m0khz/Simple_VFO/Software_Simple_VFO_Plus_V1_01/display_functions.h

 /*
 * ***********************************************************************************
 * Copyright (c) 2020  M0KHZ - Kevin Wheatley
 * 
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
 * ***********************************************************************************
*/

#include "_fonts.h"

//
//-----------------------------------------------------------------------------
//  Screensaver display
//-----------------------------------------------------------------------------
//
void splashscreen(void)
{
  
   tft.writeRect(0,0,320,240,(uint16_t*)image_240_320); // Draw a pretty picture on screen

}

void rectangle(int x, int y, int w, int d, uint16_t color) 
{
  tft.drawRect(x, y, w, d, color);
}


void display_main_screen(void)
{
  // Clear display area just in case we have 'artifacts' from Sig gen screen

  // now clear the display
  tft.fillScreen(ILI9341_BLACK);
  // draw boarder around full display
  rectangle(outline_boarder_x, outline_boarder_y, outline_boarder_w, outline_boarder_d, outline_boarder_colour);

  // draw rectangle around frequency display
 tft.drawRoundRect(main_freq_boarder_x,main_freq_boarder_y,main_freq_boarder_w,main_freq_boarder_d,3,ILI9341_DARKGREY);

  // clear frequency text area just incase there is something there!
  tft.fillRect((main_freq_boarder_x +1),(main_freq_boarder_y + 1), (main_freq_boarder_w - 3), (main_freq_boarder_d - 2), ILI9341_BLACK);

  // draw rectangle around frequency display
  tft.drawRoundRect(sub_freq_boarder_x,sub_freq_boarder_y,sub_freq_boarder_w,sub_freq_boarder_d,3,ILI9341_DARKGREY);

  // clear frequency text area just incase there is something there!
  tft.fillRect((sub_freq_boarder_x +1),(sub_freq_boarder_y + 1), (sub_freq_boarder_w - 3), (sub_freq_boarder_d - 2), ILI9341_BLACK);

   // draw rectangle around frequency display
   tft.drawRoundRect(info_boarder_x,info_boarder_y,info_boarder_w,info_boarder_d,3,ILI9341_DARKGREY);

  // Now display a user message while system is initialising
  tft.fillRect((info_boarder_x +1),(info_boarder_y + 1), (info_boarder_w - 3), (info_boarder_d - 2), ILI9341_BLACK);
  tft.setCursor(info_cursor_pos_x + 30,info_cursor_pos_y + 10); 
  tft.setTextColor(info_text_colour);
  // set frequency readout font size
  tft.setFont(DroidSansMono_12);
  tft.print("Initialising system");
  // redraw vfo lock if needed
  display_vfo_lock(); 
  
  flag.fg_ReDraw_Screen= true;
  flag.fg_A_B_changed=true;
  flag.fg_freq_Changed=true;

}

// Draw frequency multiplier bar on display
void Freq_Multi_Bar (){
if(flag.mode == false) { // were're in VFO mode so update accordingly

  if(flag.freq_multi_bar){
     
       if(u.tune_multi==1){
        tft.fillRect(20,96,220,2,ILI9341_BLACK );
        tft.fillRect(20,150,220,2,ILI9341_BLACK );
        
          if(flag.vfo_A_active==true){
            tft.fillRect(223,96,14,2,ILI9341_CYAN );
          }
          if(flag.vfo_B_active==true){
            tft.fillRect(223,150,14,2,ILI9341_CYAN );
          }  
       }
       
       if(u.tune_multi==2){
        tft.fillRect(20,96,220,2,ILI9341_BLACK );
        tft.fillRect(20,150,220,2,ILI9341_BLACK );
        
          if(flag.vfo_A_active==true){
            tft.fillRect(202,96,14,2,ILI9341_CYAN );
          }
          if(flag.vfo_B_active==true){
            tft.fillRect(202,150,14,2,ILI9341_CYAN );
          }
       }
       
       if(u.tune_multi==3){
        tft.fillRect(20,96,220,2,ILI9341_BLACK );
        tft.fillRect(20,150,220,2,ILI9341_BLACK );

           if(flag.vfo_A_active==true){
            tft.fillRect(181,96,14,2,ILI9341_CYAN );
          }
          if(flag.vfo_B_active==true){
            tft.fillRect(181,150,14,2,ILI9341_CYAN );
          }
       }
       
       if(u.tune_multi==4){
        tft.fillRect(20,96,220,2,ILI9341_BLACK );
        tft.fillRect(20,150,220,2,ILI9341_BLACK );

            if(flag.vfo_A_active==true){
            tft.fillRect(145,96,14,2,ILI9341_CYAN );
          }
          if(flag.vfo_B_active==true){
            tft.fillRect(145,150,14,2,ILI9341_CYAN );
          }    
       }
       
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
        tft.fillRect(20,150,220,2,ILI9341_BLACK );

            if(flag.fg_A_active==true){
            tft.fillRect(68,96,14,2,ILI9341_CYAN );
          }
          if(flag.fg_B_active==true){
            tft.fillRect(68,150,14,2,ILI9341_CYAN );
          }   
       }
          
    }
  }
}

void display_update_vfo(){
  
      // ------ variables used for vfo uodates etc.
      String freqt=String(u.vfo_A_value);    // Text frquency convertrd
      char F100m,F10m,Fmega,F100k,F10k,F1k,F100,F10,F1; //EachdDigit for VFO A
      char f100m,f10m,fmega,f100k,f10k,f1k,f100,f10,f1; //EachdDigit for VFO B
      int freqMulti;
      int freqlength;

      // clear frequency text area just incase there is something there!
  if((((flag.vfo_A_active==true) && (flag.freq_Changed=true)) || (flag.vfo_A_B_changed==true)) || (flag.vfo_AB_changed==true))
    
  {      
      // set frequency readout font size
      tft.setFont(DroidSansMono_24);
      if(flag.vfo_A_active==false)
      {
          tft.setTextColor(ILI9341_DARKGREY);
      }
      if(flag.vfo_A_active==true)
      {
          tft.setTextColor(main_freq_text_colour); 
      }
      tft.setCursor(main_freq_cursor_pos_x,main_freq_cursor_pos_y);
      
      // ------ Display VFO A frequency

      freqt=String(u.vfo_A_value);
      freqlength=(freqt.length());

      if(F1 !=(freqt.charAt(freqlength-1))){

          int F1_OffSet = 159;
          int F1_x = main_freq_cursor_pos_x + F1_OffSet;
          int F1_y = main_freq_cursor_pos_y ;

          tft.fillRect(F1_x,F1_y - 2,20,28,ILI9341_BLACK);
          tft.setCursor(F1_x,F1_y);
          tft.print(freqt.charAt(freqlength-1)); 
          F1 = (freqt.charAt(freqlength-1)); 
          tft.print(" Hz"); 
      }
    
      if(F10 !=(freqt.charAt(freqlength-2))){
      
          int F10_OffSet = 138;
          int F10_x = main_freq_cursor_pos_x + F10_OffSet;
          int F10_y = main_freq_cursor_pos_y ;
    
          tft.fillRect(F10_x,F10_y - 2,20,28,ILI9341_BLACK);
          tft.setCursor(F10_x,F10_y);
          tft.print(freqt.charAt(freqlength-2)); 
          F10 = (freqt.charAt(freqlength-2));
      }
     
      if(F100 !=(freqt.charAt(freqlength-3))){
      
          int F100_OffSet = 117;
          int F100_x = main_freq_cursor_pos_x + F100_OffSet;
          int F100_y = main_freq_cursor_pos_y ;
    
          tft.fillRect(F100_x,F100_y - 2,20,28,ILI9341_BLACK);
          tft.setCursor(F100_x,F100_y);
          tft.print(freqt.charAt(freqlength-3));
          F100 = (freqt.charAt(freqlength-3));
      }
     
      if(F1k !=(freqt.charAt(freqlength-4))){
      
          int F1k_OffSet = 82;
          int F1k_x = main_freq_cursor_pos_x + F1k_OffSet;
          int F1k_y = main_freq_cursor_pos_y ;
    
          tft.fillRect(F1k_x,F1k_y - 2,20,28,ILI9341_BLACK);
          tft.setCursor(F1k_x,F1k_y);
          tft.print(freqt.charAt(freqlength-4));
          // now print seperator
          tft.print(".");  
          F1k = (freqt.charAt(freqlength-4));
      }
     
      if(F10k !=(freqt.charAt(freqlength-5))){
      
          int F10k_OffSet = 61;
          int F10k_x = main_freq_cursor_pos_x + F10k_OffSet;
          int F10k_y = main_freq_cursor_pos_y ;
    
          tft.fillRect(F10k_x,F10k_y - 2,20,28,ILI9341_BLACK);
          tft.setCursor(F10k_x,F10k_y);
          tft.print(freqt.charAt(freqlength-5)); 
          F10k = (freqt.charAt(freqlength-5));
      }
     
       if(F100k !=(freqt.charAt(freqlength-6))){
        
          int F100k_OffSet = 40;
          int F100k_x = main_freq_cursor_pos_x + F100k_OffSet;
          int F100k_y = main_freq_cursor_pos_y ;
      
          tft.fillRect(F100k_x,F100k_y - 2,20,28,ILI9341_BLACK);
          tft.setCursor(F100k_x,F100k_y);
          tft.print(freqt.charAt(freqlength-6)); 
          F100k = (freqt.charAt(freqlength-6));
       }
     
       if(Fmega !=(freqt.charAt(freqlength-7))){
        
          int Fmega_OffSet = 5;
          int Fmega_x = main_freq_cursor_pos_x + Fmega_OffSet;
          int Fmega_y = main_freq_cursor_pos_y ;
      
          tft.fillRect(Fmega_x,Fmega_y - 2,20,28,ILI9341_BLACK);
          tft.setCursor(Fmega_x,Fmega_y);
          tft.print(freqt.charAt(freqlength-7));
          // now print seperator
          tft.print(".");
          Fmega = (freqt.charAt(freqlength-7));
       }
     
       if(F10m !=(freqt.charAt(freqlength-8))){
        
          int F10m_OffSet = -16;
          int F10m_x = main_freq_cursor_pos_x + F10m_OffSet;
          int F10m_y = main_freq_cursor_pos_y ;
      
          tft.fillRect(F10m_x,F10m_y - 2,20,28,ILI9341_BLACK);
          tft.setCursor(F10m_x,F10m_y);
          tft.print(freqt.charAt(freqlength-8)); 
          F10m = (freqt.charAt(freqlength-8));
       }
     
       if(F100m !=(freqt.charAt(freqlength-9))){
        
          int F100m_OffSet = -37;
          int F100m_x = main_freq_cursor_pos_x + F100m_OffSet;
          int F100m_y = main_freq_cursor_pos_y ;
      
          tft.fillRect(F100m_x,F100m_y - 2,20,28,ILI9341_BLACK);
          tft.setCursor(F100m_x,F100m_y);
          tft.print(freqt.charAt(freqlength-9)); 
          F100m = (freqt.charAt(freqlength-9));
       }
  }

  if(((((flag.vfo_B_active==true) && (flag.freq_Changed=true)) || (flag.ReDraw_Screen==true)) || (flag.vfo_A_B_changed==true)) || (flag.vfo_AB_changed==true))
  {
       // set frequency readout colour & font size
      tft.setFont(DroidSansMono_24);

      if(flag.vfo_B_active==false)
      {
          tft.setTextColor(ILI9341_DARKGREY);
      }
      if(flag.vfo_B_active==true)
      {
          tft.setTextColor(main_freq_text_colour); 
      }

      tft.setCursor(sub_freq_cursor_pos_x,main_freq_cursor_pos_y);
      
      // ------ Display VFO B frequency

      freqt=String(u.vfo_B_value);
      freqlength=(freqt.length());

      if(f1 !=(freqt.charAt(freqlength-1))){

          int f1_OffSet = 159;
          int f1_x = sub_freq_cursor_pos_x + f1_OffSet;
          int f1_y = sub_freq_cursor_pos_y ;

          tft.fillRect(f1_x,f1_y - 2,20,28,ILI9341_BLACK);
          tft.setCursor(f1_x,f1_y);
          tft.print(freqt.charAt(freqlength-1)); 
          f1 = (freqt.charAt(freqlength-1)); 
          tft.print(" Hz"); 
      }
    
      if(f10 !=(freqt.charAt(freqlength-2))){
      
          int f10_OffSet = 138;
          int f10_x = sub_freq_cursor_pos_x + f10_OffSet;
          int f10_y = sub_freq_cursor_pos_y ;
    
          tft.fillRect(f10_x,f10_y - 2,20,28,ILI9341_BLACK);
          tft.setCursor(f10_x,f10_y);
          tft.print(freqt.charAt(freqlength-2)); 
          f10 = (freqt.charAt(freqlength-2));
      }
     
      if(f100 !=(freqt.charAt(freqlength-3))){
      
          int f100_OffSet = 117;
          int f100_x = sub_freq_cursor_pos_x + f100_OffSet;
          int f100_y = sub_freq_cursor_pos_y ;
    
          tft.fillRect(f100_x,f100_y - 2,20,28,ILI9341_BLACK);
          tft.setCursor(f100_x,f100_y);
          tft.print(freqt.charAt(freqlength-3));
          f100 = (freqt.charAt(freqlength-3));
      }
     
      if(f1k !=(freqt.charAt(freqlength-4))){
      
          int f1k_OffSet = 82;
          int f1k_x = sub_freq_cursor_pos_x + f1k_OffSet;
          int f1k_y = sub_freq_cursor_pos_y ;
    
          tft.fillRect(f1k_x,f1k_y - 2,20,28,ILI9341_BLACK);
          tft.setCursor(f1k_x,f1k_y);
          tft.print(freqt.charAt(freqlength-4));
          // now print seperator
          tft.print(".");  
          f1k = (freqt.charAt(freqlength-4));
      }
     
      if(f10k !=(freqt.charAt(freqlength-5))){
      
          int f10k_OffSet = 61;
          int f10k_x = sub_freq_cursor_pos_x + f10k_OffSet;
          int f10k_y = sub_freq_cursor_pos_y ;
    
          tft.fillRect(f10k_x,f10k_y - 2,20,28,ILI9341_BLACK);
          tft.setCursor(f10k_x,f10k_y);
          tft.print(freqt.charAt(freqlength-5)); 
          f10k = (freqt.charAt(freqlength-5));
      }
     
       if(f100k !=(freqt.charAt(freqlength-6))){
        
          int f100k_OffSet = 40;
          int f100k_x = sub_freq_cursor_pos_x + f100k_OffSet;
          int f100k_y = sub_freq_cursor_pos_y ;
      
          tft.fillRect(f100k_x,f100k_y - 2,20,28,ILI9341_BLACK);
          tft.setCursor(f100k_x,f100k_y);
          tft.print(freqt.charAt(freqlength-6)); 
          f100k = (freqt.charAt(freqlength-6));
       }
     
       if(fmega !=(freqt.charAt(freqlength-7))){
        
          int fmega_OffSet = 5;
          int fmega_x = sub_freq_cursor_pos_x + fmega_OffSet;
          int fmega_y = sub_freq_cursor_pos_y ;
      
          tft.fillRect(fmega_x,fmega_y - 2,20,28,ILI9341_BLACK);
          tft.setCursor(fmega_x,fmega_y);
          tft.print(freqt.charAt(freqlength-7));
          // now print seperator
          tft.print(".");
          fmega = (freqt.charAt(freqlength-7));
       }
     
       if(f10m !=(freqt.charAt(freqlength-8))){
        
          int f10m_OffSet = -16;
          int f10m_x = sub_freq_cursor_pos_x + f10m_OffSet;
          int f10m_y = sub_freq_cursor_pos_y ;
      
          tft.fillRect(f10m_x,f10m_y - 2,20,28,ILI9341_BLACK);
          tft.setCursor(f10m_x,f10m_y);
          tft.print(freqt.charAt(freqlength-8)); 
          f10m = (freqt.charAt(freqlength-8));
       }
     
       if(f100m !=(freqt.charAt(freqlength-9))){
        
          int f100m_OffSet = -37;
          int f100m_x = sub_freq_cursor_pos_x + f100m_OffSet;
          int f100m_y = sub_freq_cursor_pos_y ;
      
          tft.fillRect(f100m_x,f100m_y - 2,20,28,ILI9341_BLACK);
          tft.setCursor(f100m_x,f100m_y);
          tft.print(freqt.charAt(freqlength-9)); 
          f100m = (freqt.charAt(freqlength-9));
       }
       
      flag.ReDraw_Screen= false;
      flag.vfo_A_B_changed=false;
      delay(50);
      
  }
}
