m0khz/Simple_VFO/Software_Simple_VFO_Plus_V1_01/_fonts.h

// This is an aggregation of DroidSansMono and AwesomeF000
// monospace fonts from the ILI9431_t3 Fonts Library
// If the fonts have been installed in ILI9341_t3 library, then this should be
// deleted and the fonts #included in PSWR_T.h instead.

#ifndef _ILI9341_t3_fonts_
#define _ILI9341_t3_fonts_

#include "ILI9341_t3.h"

#ifdef __cplusplus
extern "C" {
#endif

extern const ILI9341_t3_font_t DroidSansMono_8;
extern const ILI9341_t3_font_t DroidSansMono_9;
extern const ILI9341_t3_font_t DroidSansMono_10;
extern const ILI9341_t3_font_t DroidSansMono_11;
extern const ILI9341_t3_font_t DroidSansMono_12;
extern const ILI9341_t3_font_t DroidSansMono_13;
extern const ILI9341_t3_font_t DroidSansMono_14;
extern const ILI9341_t3_font_t DroidSansMono_16;
extern const ILI9341_t3_font_t DroidSansMono_18;
extern const ILI9341_t3_font_t DroidSansMono_20;
extern const ILI9341_t3_font_t DroidSansMono_24;
extern const ILI9341_t3_font_t DroidSansMono_28;
extern const ILI9341_t3_font_t DroidSansMono_32;
extern const ILI9341_t3_font_t DroidSansMono_40;
extern const ILI9341_t3_font_t DroidSansMono_48;
extern const ILI9341_t3_font_t DroidSansMono_60;
extern const ILI9341_t3_font_t DroidSansMono_72;
extern const ILI9341_t3_font_t DroidSansMono_96;

extern const ILI9341_t3_font_t AwesomeF000_8;
extern const ILI9341_t3_font_t AwesomeF000_9;
extern const ILI9341_t3_font_t AwesomeF000_10;
extern const ILI9341_t3_font_t AwesomeF000_11;
extern const ILI9341_t3_font_t AwesomeF000_12;
extern const ILI9341_t3_font_t AwesomeF000_13;
extern const ILI9341_t3_font_t AwesomeF000_14;
extern const ILI9341_t3_font_t AwesomeF000_16;
extern const ILI9341_t3_font_t AwesomeF000_18;
extern const ILI9341_t3_font_t AwesomeF000_20;
extern const ILI9341_t3_font_t AwesomeF000_24;
extern const ILI9341_t3_font_t AwesomeF000_28;
extern const ILI9341_t3_font_t AwesomeF000_32;
extern const ILI9341_t3_font_t AwesomeF000_40;
extern const ILI9341_t3_font_t AwesomeF000_48;
extern const ILI9341_t3_font_t AwesomeF000_60;
extern const ILI9341_t3_font_t AwesomeF000_72;
extern const ILI9341_t3_font_t AwesomeF000_96;

#ifdef __cplusplus
} // extern "C"
#endif

#endif
